Jazor25/esphome-smart-doorbell-project/img/mounting_1.jpg

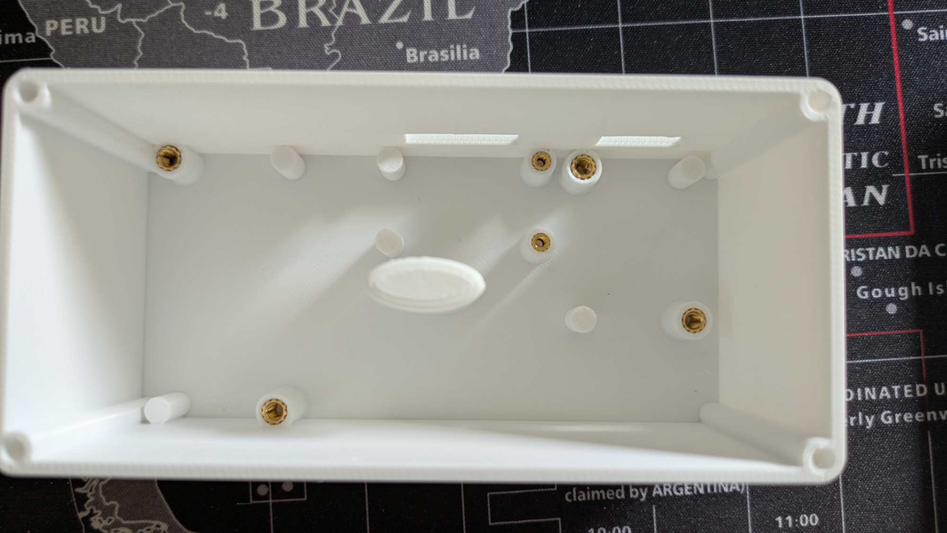
img/mounting_1.jpg
