Jazor25/esphome-smart-doorbell-project/img/mounting_2.jpg

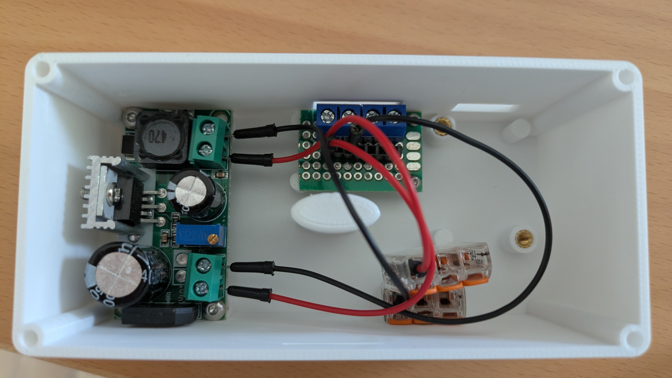
img/mounting_2.jpg
